SeanP2001/ATtiny_Handheld_Games_Console/ButtonTest/Button.h

#ifndef _BUTTON_H_
#define _BUTTON_H_

#include <Arduino.h>

class Button{
public:
  int pin;                                     // button pin

  uint8_t lowerBound;
  uint8_t upperBound;
  
  uint8_t buttonValue = 0;                     // button analogue output value
  
  int buttonState;                             // Current state of the button
  int lastButtonState = LOW;                   // The last state of the button
  
  unsigned long stateChangeTime = 0;           // When the button changed state
  
  unsigned long debounceDelay = 200;            // debounce time

  Button(int _pin, uint8_t _lowerBound, uint8_t _upperBound);

  bool isPressed();
};


#endif // _BUTTON_H_
